ben-wallis/co2piggyback/sa1200p/images/20230520_150858.jpg

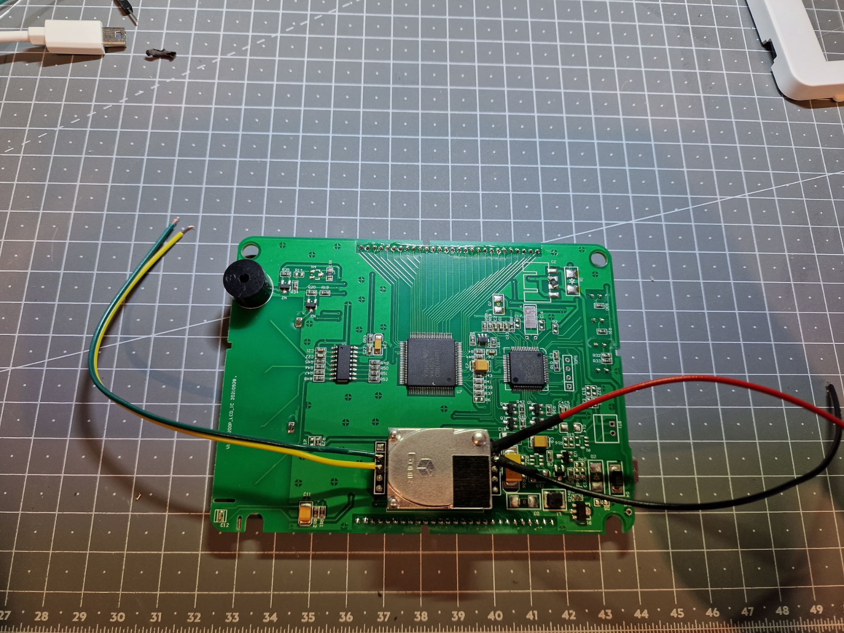
sa1200p/images/20230520_150858.jpg
